brunob45/watch/PCB/v4.6/1.png

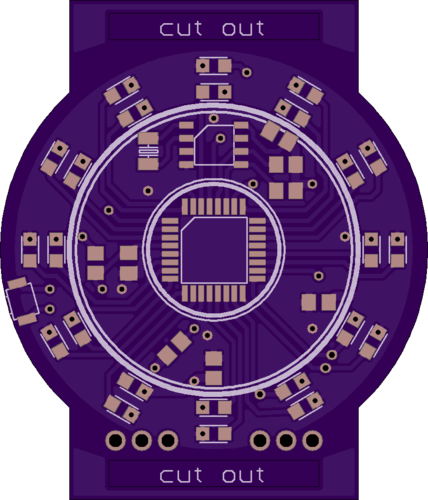
PCB/v4.6/1.png
