brunob45/watch/PCB/v4.6/2.png

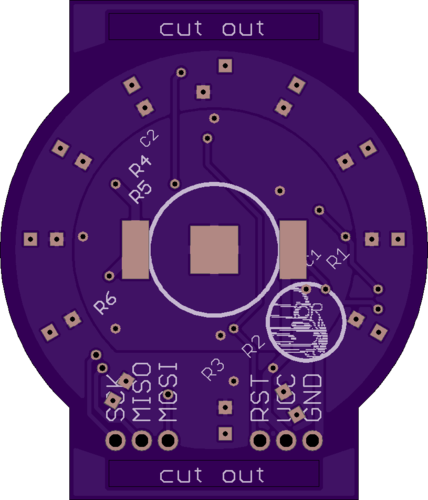
PCB/v4.6/2.png
