brunob45/watch/PCB/v4.6/3.png

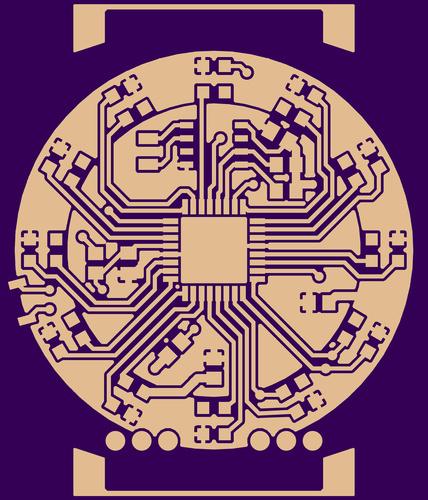
PCB/v4.6/3.png
