brunob45/watch/PCB/v4.6/4.png

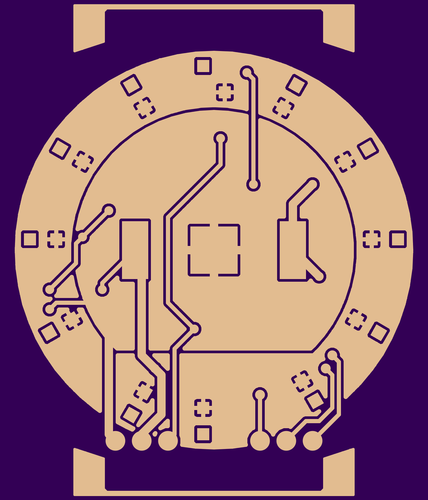
PCB/v4.6/4.png
